BrandonMitchell1920/Z80-Calculator/images/20260830_152253.jpg

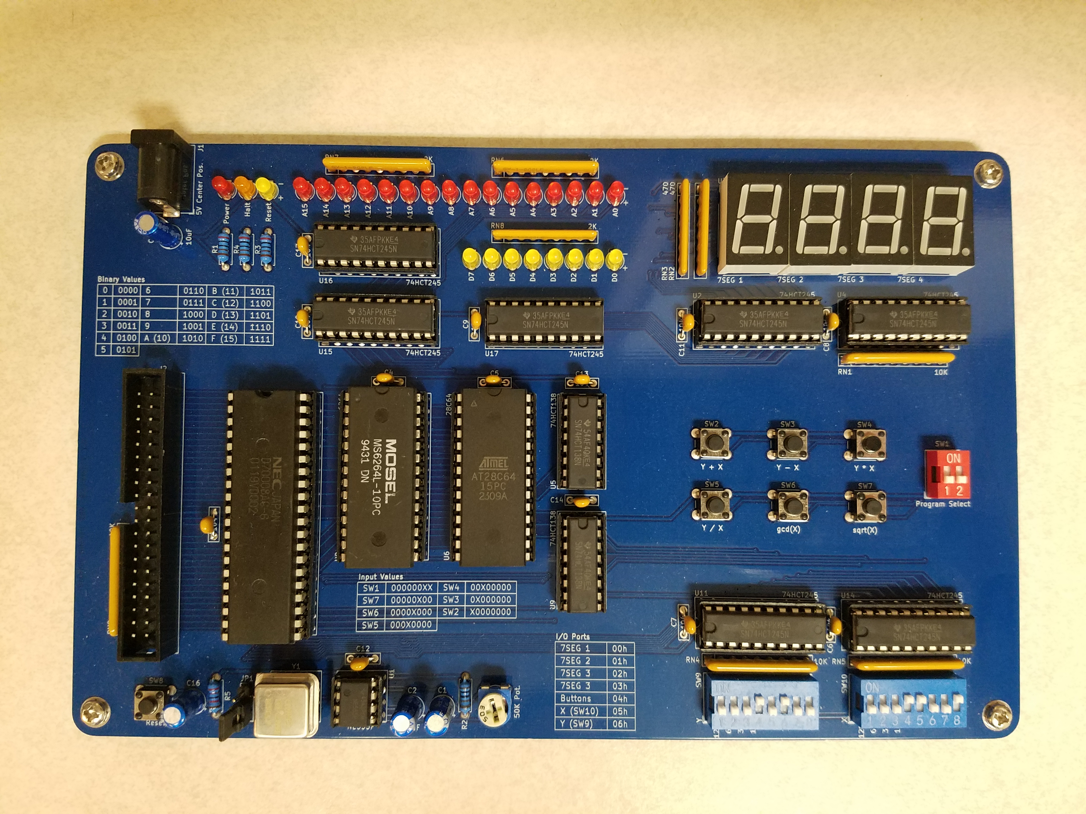
images/20260830_152253.jpg
